xx0x/sw63/code/src/dev/AdcInput.hpp

/*
MIT License

Copyright (c) 2026 Vaclav Mach (xx0x)

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
THE SOFTWARE IS PROVIDED "AS IS", WITHOUT WARRANTY OF ANY KIND, EXPRESS OR
IMPLIED, INCLUDING BUT NOT LIMITED TO THE WARRANTIES OF MERCHANTABILITY,
FITNESS FOR A PARTICULAR PURPOSE AND NONINFRINGEMENT. IN NO EVENT SHALL THE
AUTHORS OR COPYRIGHT HOLDERS BE LIABLE FOR ANY CLAIM, DAMAGES OR OTHER
LIABILITY, WHETHER IN AN ACTION OF CONTRACT, TORT OR OTHERWISE, ARISING FROM,
OUT OF OR IN CONNECTION WITH THE SOFTWARE OR THE USE OR OTHER DEALINGS IN THE
SOFTWARE.
*/

#pragma once

#include <optional>
#include "stm32l0xx_hal.h"

/**
 * @brief Reads ADC channels in single-shot mode.
 * @author Vaclav Mach (xx0x)
 * @date 2026-02-02
 */
class AdcInput
{
public:
    /**
     * @brief Maximum 12-bit ADC conversion value.
     */
    static constexpr uint16_t kResolution = 4095; // 12-bit max value

    /**
     * @brief Defines GPIO and channel mapping for an ADC input.
     */
    struct Config
    {
        GPIO_TypeDef *port;
        uint16_t pin;
        uint32_t channel;
    };

    /**
     * @brief Initializes ADC input with selected channel configuration.
     * @param config ADC port, pin, and channel configuration.
     * @return True when initialization succeeds.
     */
    bool Init(const Config &config)
    {
        config_ = config;

        if (!InitAdc())
        {
            return false;
        }

        // Configure GPIO pin as analog input (only for external channels)
        if (config_.port != nullptr)
        {
            GPIO_InitTypeDef GPIO_InitStruct = {};
            GPIO_InitStruct.Pin = config_.pin;
            GPIO_InitStruct.Mode = GPIO_MODE_ANALOG;
            GPIO_InitStruct.Pull = GPIO_NOPULL;
            HAL_GPIO_Init(config_.port, &GPIO_InitStruct);
        }

        initialized_ = true;
        return true;
    }

    /**
     * @brief Deinitializes ADC input and associated GPIO.
     * @return True when deinitialization succeeds.
     */
    bool DeInit()
    {
        if (!initialized_)
        {
            return false;
        }

        // Deinitialize GPIO (only for external channels)
        if (config_.port != nullptr)
        {
            HAL_GPIO_DeInit(config_.port, config_.pin);
        }
        DeInitAdc();
        initialized_ = false;
        return true;
    }

    /**
     * @brief Performs one ADC conversion.
     * @return ADC value or std::nullopt on failure.
     */
    std::optional<uint16_t> ReadSingleShot()
    {
        if (!initialized_)
        {
            return std::nullopt;
        }

        // Configure ADC channel
        // STM32L0 keeps a sequence of enabled channels in CHSELR.
        // Ensure only the requested channel is selected to avoid reading a different rank.
        hadc_.Instance->CHSELR = 0; // Clear all previously selected channels
        ADC_ChannelConfTypeDef sConfig = {};
        sConfig.Channel = config_.channel;
        sConfig.Rank = ADC_RANK_CHANNEL_NUMBER;
        if (HAL_ADC_ConfigChannel(&hadc_, &sConfig) != HAL_OK)
        {
            return std::nullopt;
        }

        // Start ADC conversion
        if (HAL_ADC_Start(&hadc_) != HAL_OK)
        {
            return std::nullopt;
        }

        // Wait for conversion completion (timeout: 10ms)
        if (HAL_ADC_PollForConversion(&hadc_, 10) != HAL_OK)
        {
            HAL_ADC_Stop(&hadc_);
            return std::nullopt;
        }

        // Get conversion result
        uint32_t result = HAL_ADC_GetValue(&hadc_);

        // Stop ADC
        HAL_ADC_Stop(&hadc_);

        return static_cast<uint16_t>(result);
    }

private:
    /**
     * @brief Initializes shared ADC peripheral.
     * @return True when peripheral initialization succeeds.
     */
    static bool InitAdc()
    {
        if (init_count_ > 0)
        {
            init_count_++;
            return true;
        }

        // Enable ADC clock
        __HAL_RCC_ADC1_CLK_ENABLE();

        // Configure ADC
        hadc_.Instance = ADC1;
        hadc_.Init.ClockPrescaler = ADC_CLOCK_SYNC_PCLK_DIV2;
        hadc_.Init.Resolution = ADC_RESOLUTION_12B;
        hadc_.Init.DataAlign = ADC_DATAALIGN_RIGHT;
        hadc_.Init.ScanConvMode = 0x00000000U; // ADC_SCAN_DISABLE for STM32L0
        hadc_.Init.EOCSelection = ADC_EOC_SINGLE_CONV;
        hadc_.Init.LowPowerAutoWait = DISABLE;
        hadc_.Init.LowPowerAutoPowerOff = DISABLE;
        hadc_.Init.ContinuousConvMode = DISABLE;
        hadc_.Init.DiscontinuousConvMode = DISABLE;
        hadc_.Init.ExternalTrigConv = ADC_SOFTWARE_START;
        hadc_.Init.ExternalTrigConvEdge = ADC_EXTERNALTRIGCONVEDGE_NONE;
        hadc_.Init.DMAContinuousRequests = DISABLE;
        hadc_.Init.Overrun = ADC_OVR_DATA_OVERWRITTEN;
        hadc_.Init.LowPowerFrequencyMode = DISABLE;
        hadc_.Init.SamplingTime = ADC_SAMPLETIME_79CYCLES_5;
        hadc_.Init.OversamplingMode = DISABLE;

        if (HAL_ADC_Init(&hadc_) != HAL_OK)
        {
            return false;
        }

        // Calibrate ADC
        if (HAL_ADCEx_Calibration_Start(&hadc_, ADC_SINGLE_ENDED) != HAL_OK)
        {
            return false;
        }

        init_count_++;
        return true;
    }

    /**
     * @brief Deinitializes shared ADC peripheral when unused.
     */
    static void DeInitAdc()
    {
        init_count_--;
        if (init_count_ == 0)
        {
            HAL_ADC_DeInit(&hadc_);
        }
    }

    Config config_;
    bool initialized_ = false;

    static inline ADC_HandleTypeDef hadc_;
    static inline int init_count_;
};
