xx0x/sw63/code/src/dev/Button.cpp

#include "Button.hpp"
#include "dev/System.hpp"

void Button::Update()
{
    now_pressed_ = System::GetRawButtonState();
    uint32_t current_time = System::Millis();

    // Reset event flags at the beginning of each update
    ResetEvents();

    // State transitions
    if (!prev_pressed_ && now_pressed_)
    {
        // Button just pressed
        state_ = State::PRESSED;
        press_start_time_ = current_time;
        medium_triggered_ = false;
        long_triggered_ = false;

        // Fire short press immediately on press
        events_[Event::JUST_PRESSED] = true;
    }
    else if (prev_pressed_ && !now_pressed_)
    {
        // Button just released 
        uint32_t press_duration = current_time - press_start_time_;
        release_time_ = current_time;

        if (state_ == State::PRESSED)
        {
            if (press_duration < kMediumPressThresholdMs) // Less than 2 seconds
            {
                events_[Event::JUST_RELEASED] = true;
                press_count_++;

                if (press_count_ == 1)
                {
                    // First press
                    first_press_time_ = release_time_;
                    state_ = State::WAITING_FOR_MULTI;
                }
                else if (press_count_ == kMultiPressCount)
                {
                    // Check if all presses were within the multipress window
                    if ((release_time_ - first_press_time_) <= (kMultiPressWindowMs * kMultiPressCount))
                    {
                        events_[Event::MULTI_PRESS] = true;
                        // Don't fire short press for multipress
                        // Don't reset state - continue accepting more presses but ignore them
                    }
                    else
                    {
                        ResetState();
                    }
                }
                else if (press_count_ > kMultiPressCount)
                {
                    // Ignore subsequent presses after multipress - no events fired
                    if ((release_time_ - first_press_time_) > (kMultiPressWindowMs * kMultiPressCount))
                    {
                        ResetState();
                    }
                }
            }
            else
            {
                // Long press was already handled during holding
                ResetState();
            }
        }
    }

    // Handle holding states
    if (state_ == State::PRESSED && now_pressed_)
    {
        uint32_t press_duration = current_time - press_start_time_;

        if (press_duration >= kLongPressThresholdMs && !long_triggered_)
        {
            // Long press (5+ seconds)
            events_[Event::LONG_PRESS] = true;
            long_triggered_ = true;
        }
        else if (press_duration >= kMediumPressThresholdMs && !medium_triggered_)
        {
            // Medium press (2+ seconds)
            events_[Event::MEDIUM_PRESS] = true;
            medium_triggered_ = true;
        }
    }

    // Handle timeout for waiting states
    if (state_ == State::WAITING_FOR_MULTI)
    {
        if (press_count_ >= kMultiPressCount)
        {
            // Wait for more presses or timeout for multi-press
            if ((current_time - first_press_time_) > (kMultiPressWindowMs * kMultiPressCount))
            {
                ResetState();
            }
        }
        else if (press_count_ == 1)
        {
            // Wait for potential multi press
            if ((current_time - release_time_) > kMultiPressWindowMs)
            {
                ResetState();
            }
        }
    }

    prev_pressed_ = now_pressed_;
}

bool Button::Happened(Event event)
{
    return events_[event];
}

bool Button::PreventSleep()
{
    return now_pressed_;
}

void Button::ResetEvents()
{
    events_.fill(false);
}

void Button::ResetState()
{
    state_ = State::IDLE;
    press_count_ = 0;
    medium_triggered_ = false;
    long_triggered_ = false;
}
