xx0x/sw63/code/src/tusb_config.h

#pragma once

#include "stm32l0xx_hal.h"

//--------------------------------------------------------------------
// Board Specific Configuration
//--------------------------------------------------------------------

// RCC Clock
#define CFG_BOARD_RCC_HSI48M 1

//--------------------------------------------------------------------
// COMMON CONFIGURATION
//--------------------------------------------------------------------

// defined by board.mk
#ifndef CFG_TUSB_MCU
#error CFG_TUSB_MCU must be defined
#endif

// CFG_TUSB_DEBUG is defined by compiler in DEBUG build
#ifndef CFG_TUSB_DEBUG
#define CFG_TUSB_DEBUG 0
#endif

// Port 0 is device mode
#define CFG_TUSB_RHPORT0_MODE   OPT_MODE_DEVICE

/* USB DMA on some MCUs can only access a specific SRAM region with restriction on alignment. */
#define CFG_TUSB_MEM_SECTION
#define CFG_TUSB_MEM_ALIGN __attribute__ ((aligned(4)))

//--------------------------------------------------------------------
// DEVICE CONFIGURATION
//--------------------------------------------------------------------

#define CFG_TUD_ENABLED           1

#ifndef CFG_TUD_ENDPOINT0_SIZE
#define CFG_TUD_ENDPOINT0_SIZE 64
#endif

//------------- CLASS -------------//
#define CFG_TUD_CDC               1
#define CFG_TUD_MSC               0
#define CFG_TUD_HID               0
#define CFG_TUD_MIDI              0
#define CFG_TUD_VENDOR            0

// CDC FIFO size of TX and RX
#define CFG_TUD_CDC_RX_BUFSIZE    128
#define CFG_TUD_CDC_TX_BUFSIZE    128

//--------------------------------------------------------------------
// HOST CONFIGURATION
//--------------------------------------------------------------------

// Size of buffer to hold descriptors and other data used for enumeration
#define CFG_TUH_ENUMERATION_BUFSIZE 256

#define CFG_TUH_HUB 0
#define CFG_TUH_CDC 0
#define CFG_TUH_HID 0
#define CFG_TUH_MSC 0
#define CFG_TUH_VENDOR 0

// max device support (excluding hub device)
#define CFG_TUH_DEVICE_MAX 0
