xx0x/sw63/code/sw63-rust/build.rs

use std::env;
use std::fs::File;
use std::io::Write;
use std::path::PathBuf;

fn main() {
    // Put the linker script somewhere the linker can find it
    let out = &PathBuf::from(env::var_os("OUT_DIR").unwrap());
    File::create(out.join("memory.x"))
        .unwrap()
        .write_all(include_bytes!("memory.x"))
        .unwrap();
    println!("cargo:rustc-link-search={}", out.display());

    // Only re-run the build script when memory.x is changed
    println!("cargo:rerun-if-changed=memory.x");
}
